NilsM17/all-screen-keyboard-Raspberry/3Dmodels/individualkeys/key29.step

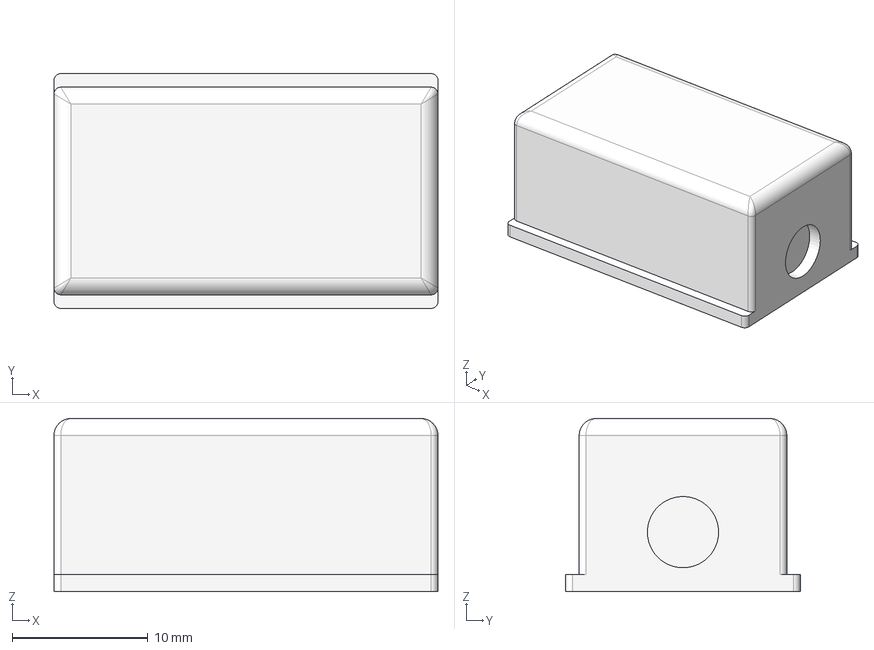
[picture p21: CAD file, 2025-07-11]
3Dmodels/individualkeys/key29.step
28.3 x 17.3 x 12.8 mm
