NilsM17/all-screen-keyboard-Raspberry/3Dmodels/individualkeys/key24.5.step

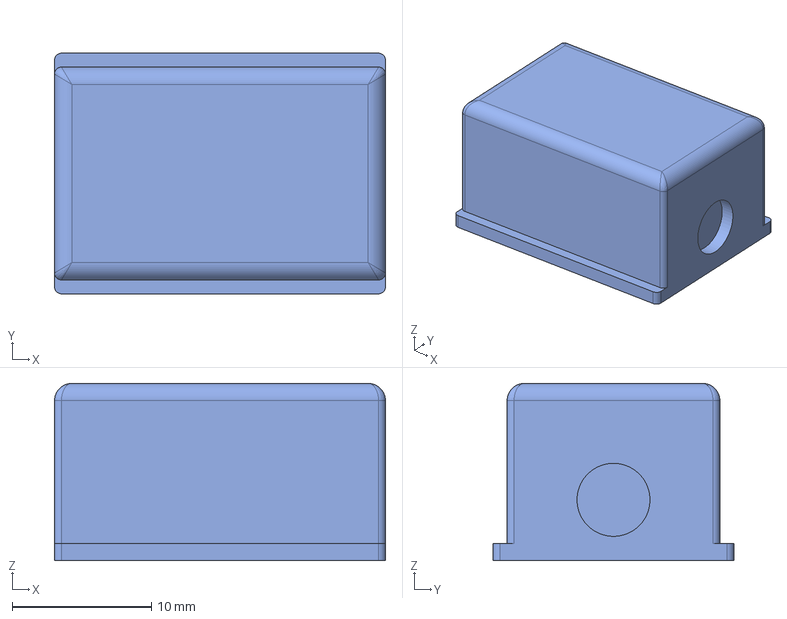
[picture p22: CAD file, 2025-07-11]
3Dmodels/individualkeys/key24.5.step
23.8 x 17.3 x 12.8 mm
