NilsM17/all-screen-keyboard-Raspberry/3Dmodels/individualkeys/key46.step

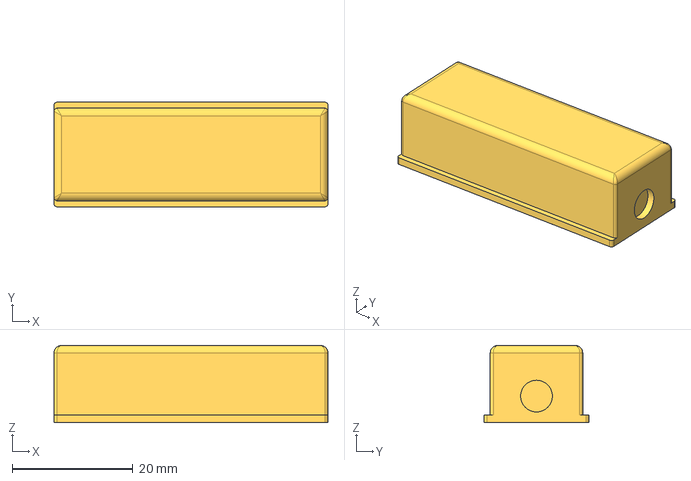
[picture p23: CAD file, 2025-07-11]
3Dmodels/individualkeys/key46.step
45.3 x 17.3 x 12.8 mm
