NilsM17/all-screen-keyboard-Raspberry/3Dmodels/individualkeys/key16.step

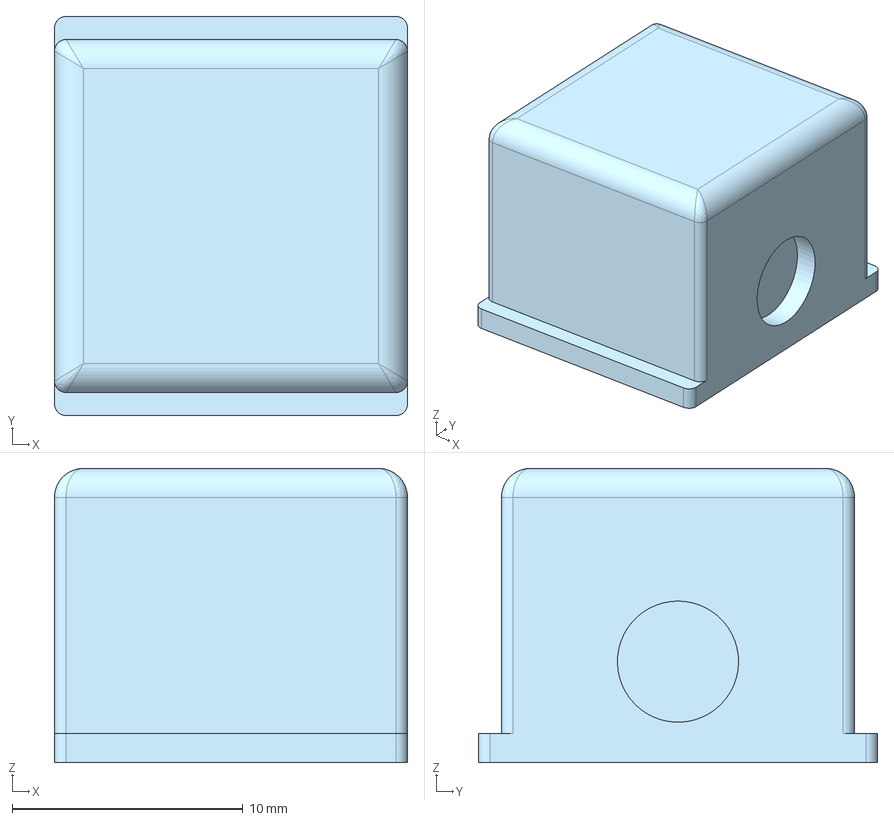
[picture p24: CAD file, 2025-07-11]
3Dmodels/individualkeys/key16.step
15.3 x 17.3 x 12.8 mm
