NilsM17/all-screen-keyboard-Raspberry/PCB/keyboard-KiCad/keyboard.kicad_sch

## KiCad design PCB/keyboard-KiCad/keyboard.kicad_sch (2025-07-11)

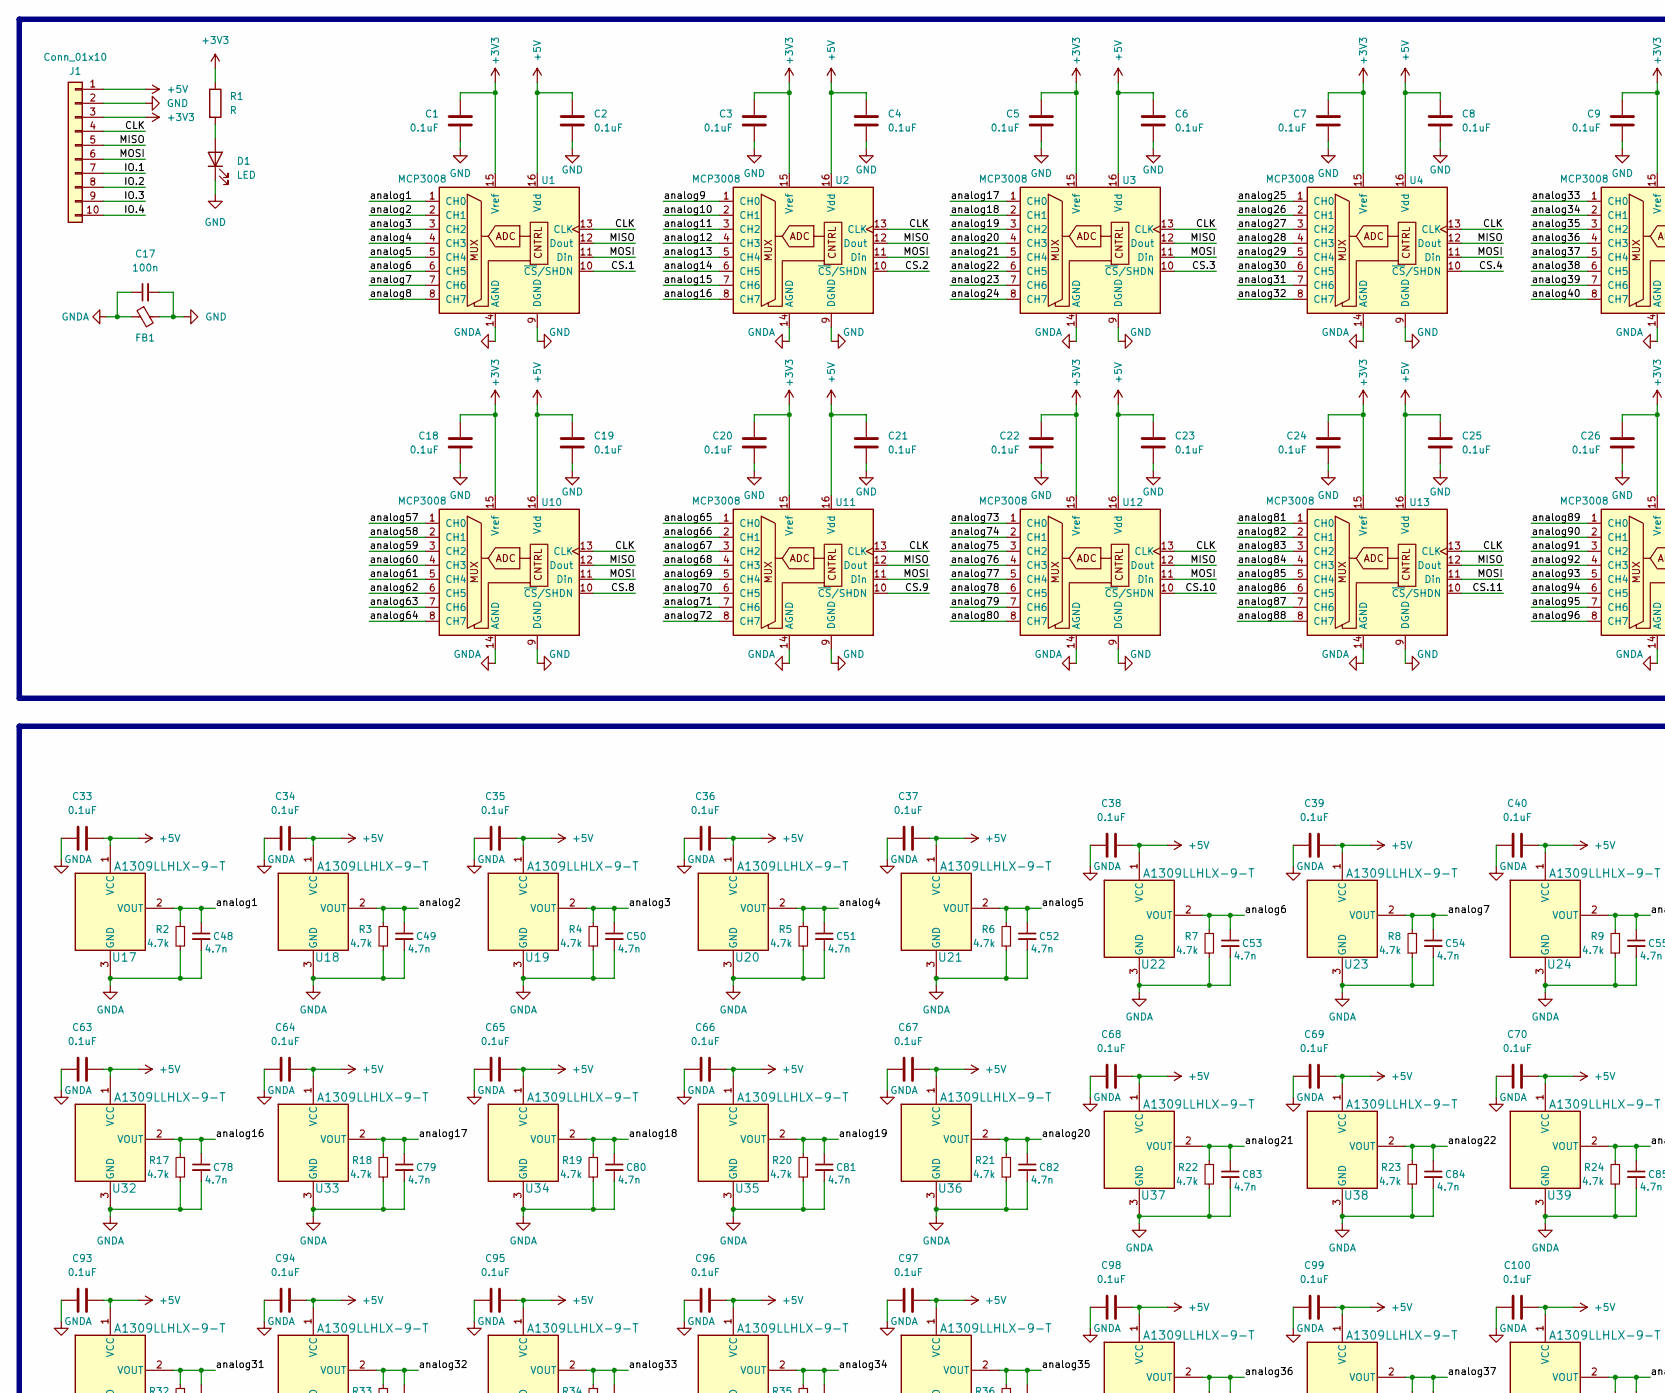
[picture p25: schematic keyboard.kicad_sch, part in row 1, column 1]

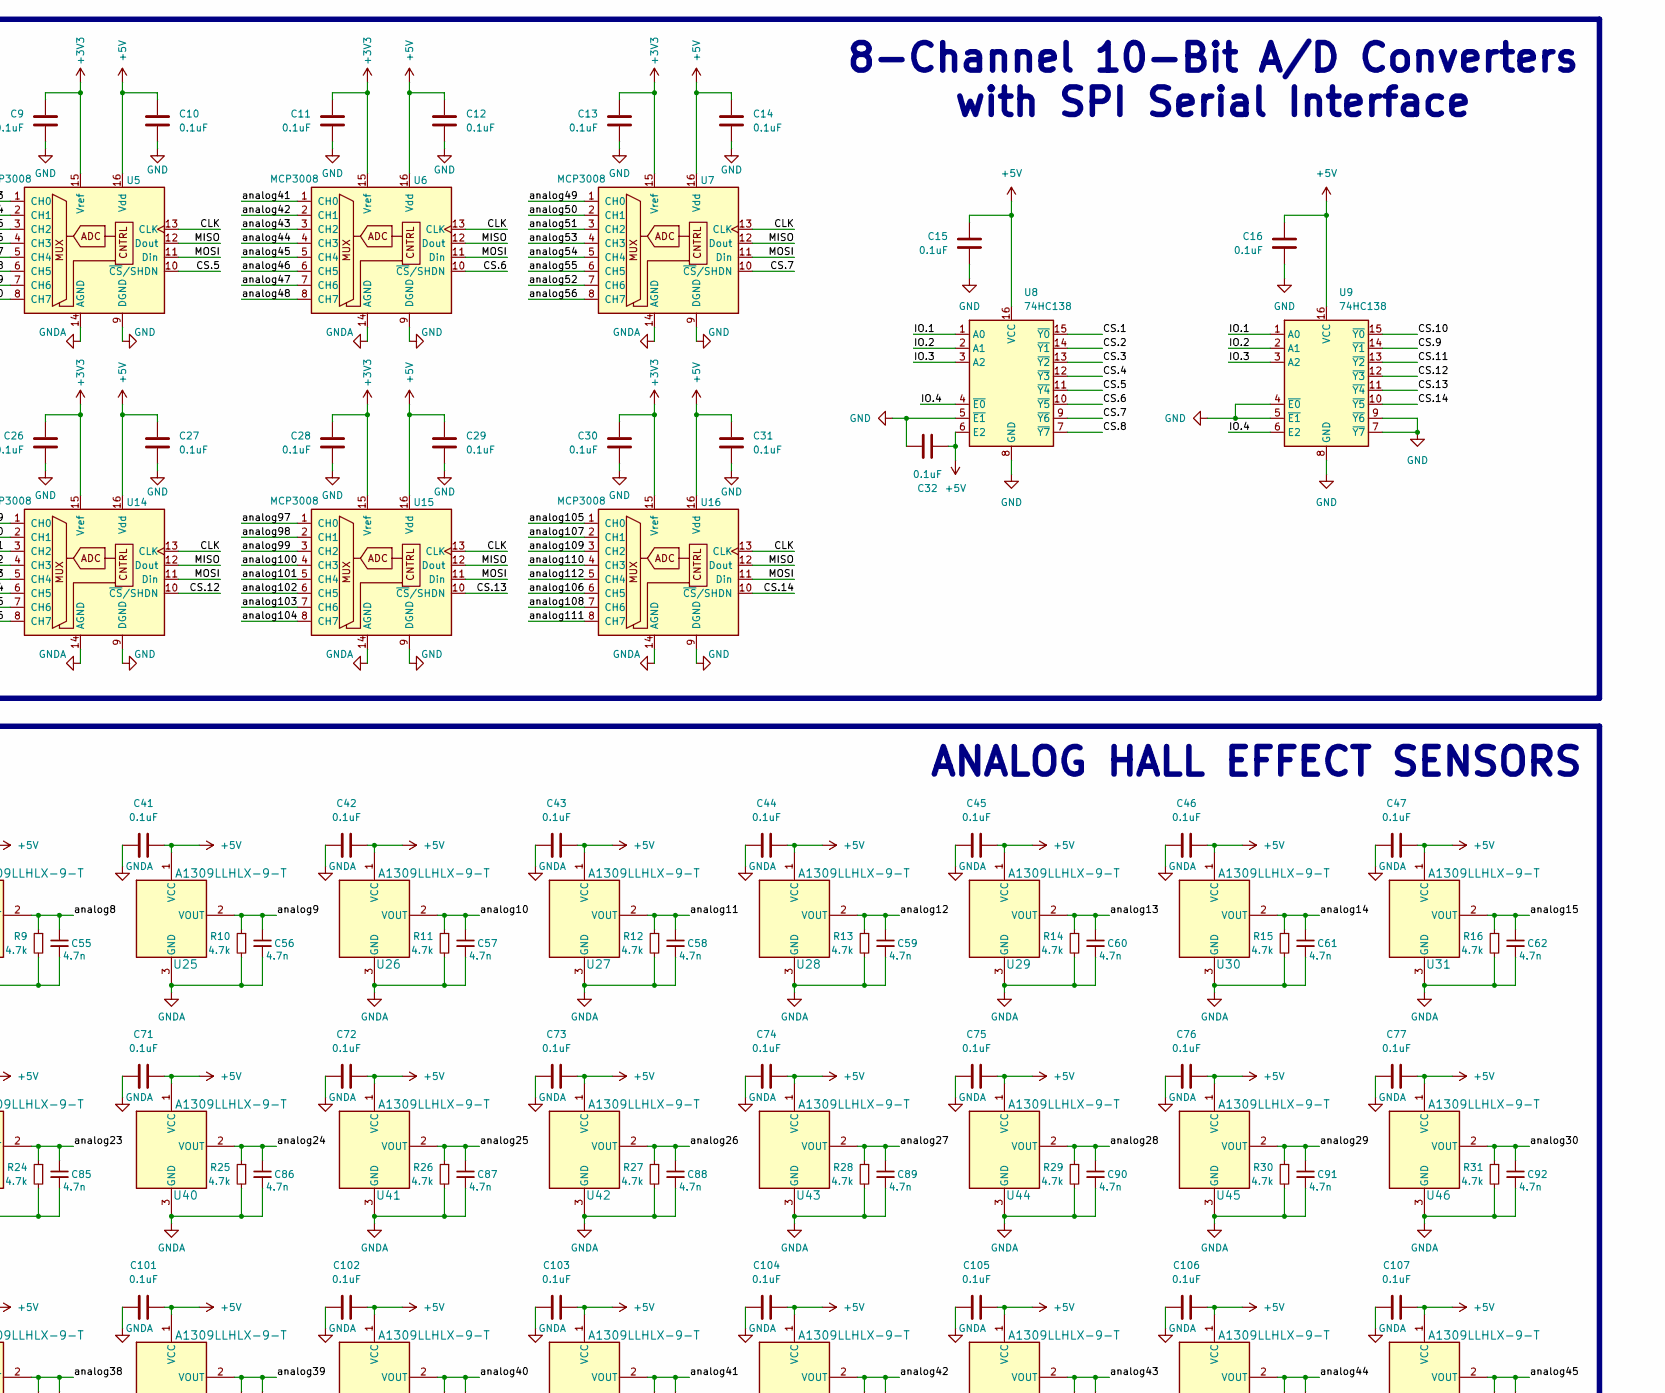
[picture p26: schematic keyboard.kicad_sch, part in row 1, column 2]

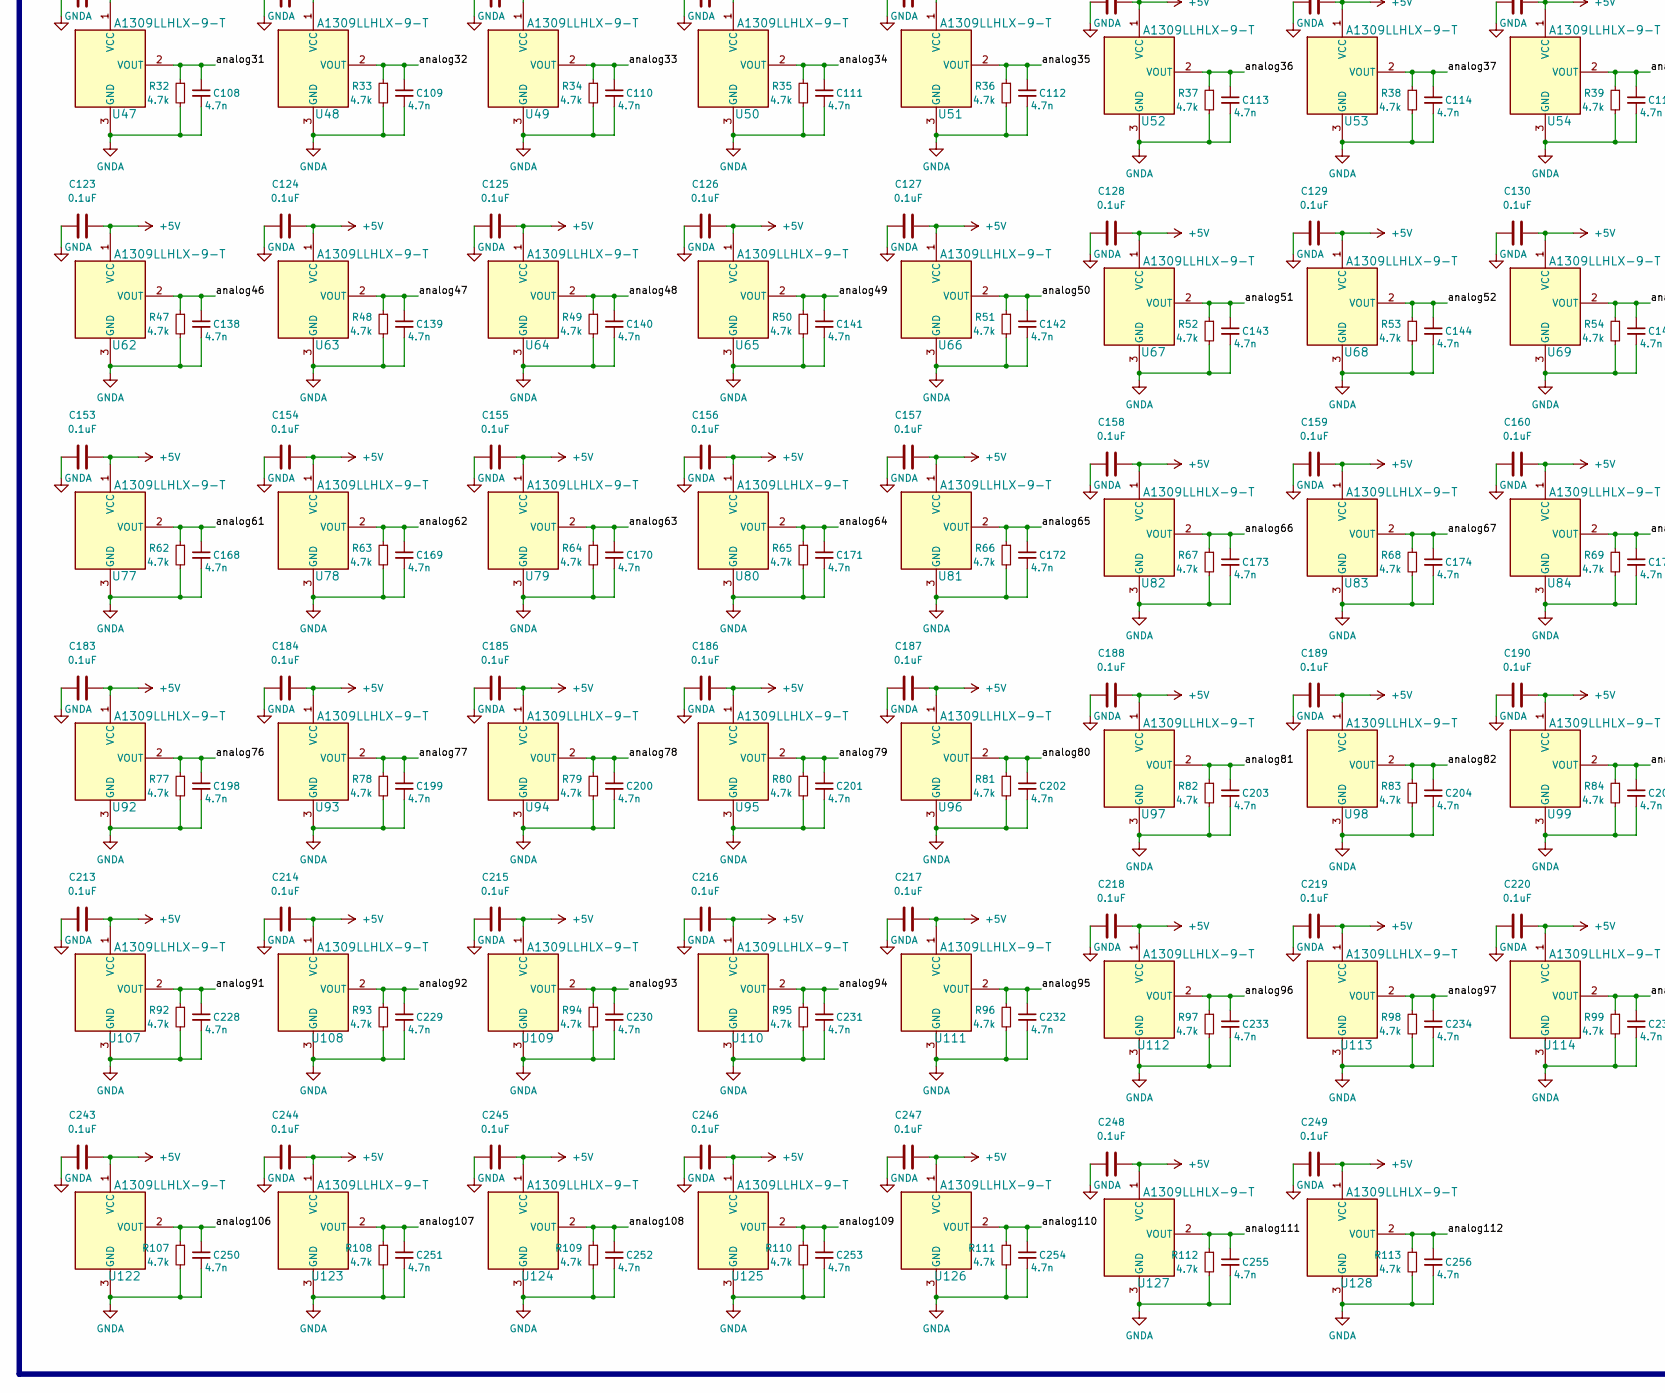
[picture p27: schematic keyboard.kicad_sch, part in row 2, column 1]

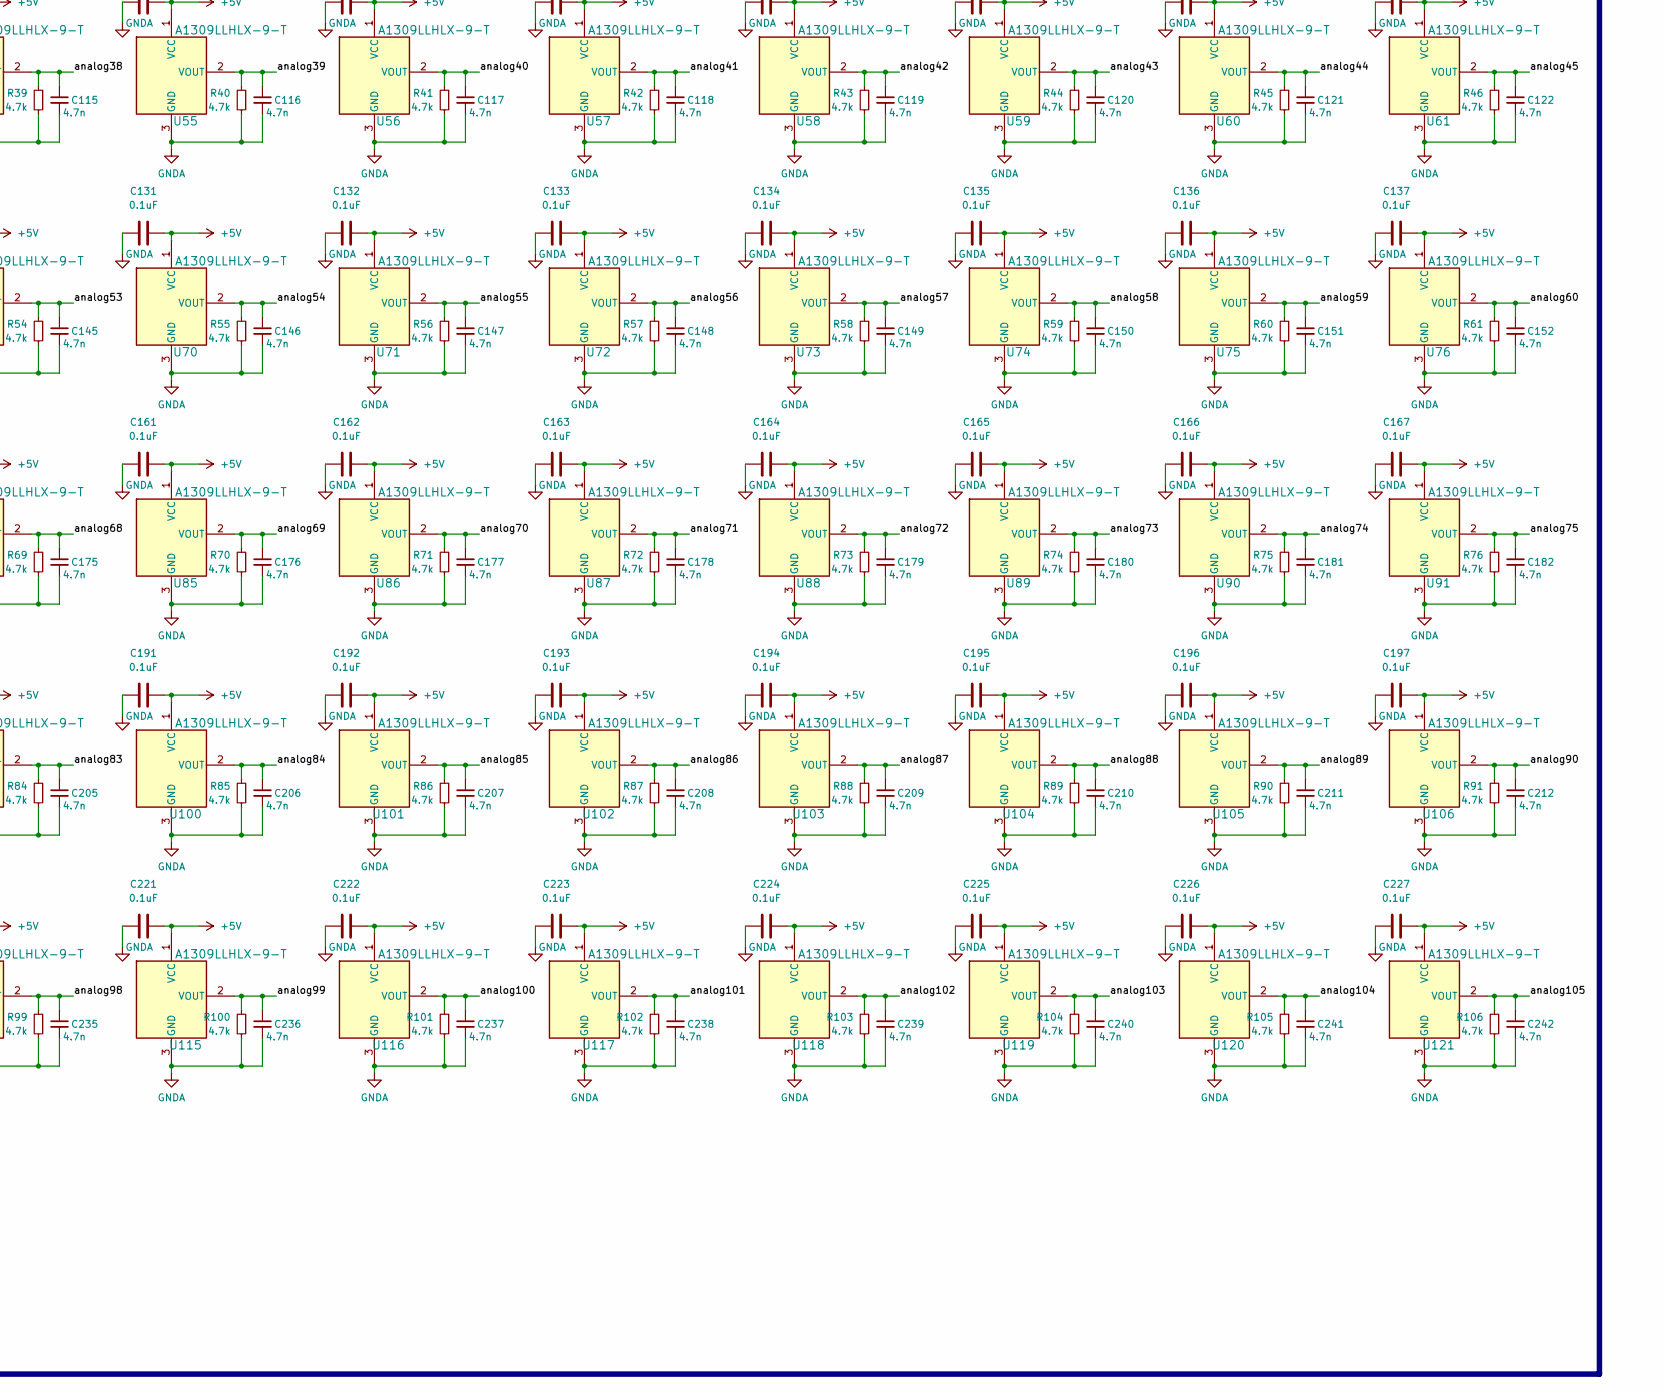
[picture p28: schematic keyboard.kicad_sch, part in row 2, column 2]

Parts:
C1, C2, C3, C4, C5, C6, C7, C8, C9, C10, C11, C12, C13, C14, C15, C16, C18, C19, C20, C21, C22, C23, C24, C25, C26, C27, C28, C29, C30, C31, C32, C33, C34, C35, C36, C37, C38, C39, C40, C41, C42, C43, C44, C45, C46, C47, C63, C64, C65, C66, C67, C68, C69, C70, C71, C72, C73, C74, C75, C76, C77, C93, C94, C95, C96, C97, C98, C99, C100, C101, C102, C103, C104, C105, C106, C107, C123, C124, C125, C126, C127, C128, C129, C130, C131, C132, C133, C134, C135, C136, C137, C153, C154, C155, C156, C157, C158, C159, C160, C161, C162, C163, C164, C165, C166, C167, C183, C184, C185, C186, C187, C188, C189, C190, C191, C192, C193, C194, C195, C196, C197, C213, C214, C215, C216, C217, C218, C219, C220, C221, C222, C223, C224, C225, C226, C227, C243, C244, C245, C246, C247, C248, C249: 0.1uF; C_0603_1608Metric
C17: 100n; C_0603_1608Metric
C48, C49, C50, C51, C52, C53, C54, C55, C56, C57, C58, C59, C60, C61, C62, C78, C79, C80, C81, C82, C83, C84, C85, C86, C87, C88, C89, C90, C91, C92, C108, C109, C110, C111, C112, C113, C114, C115, C116, C117, C118, C119, C120, C121, C122, C138, C139, C140, C141, C142, C143, C144, C145, C146, C147, C148, C149, C150, C151, C152, C168, C169, C170, C171, C172, C173, C174, C175, C176, C177, C178, C179, C180, C181, C182, C198, C199, C200, C201, C202, C203, C204, C205, C206, C207, C208, C209, C210, C211, C212, C228, C229, C230, C231, C232, C233, C234, C235, C236, C237, C238, C239, C240, C241, C242, C250, C251, C252, C253, C254, C255, C256: 4.7n; C_0603_1608Metric
D1: LED; LED_0603_1608Metric
FB1: FerriteBead_Small; L_0603_1608Metric
J1: Conn_01x10; PinHeader_1x10_P2.54mm_Vertical
R1: R; R_0603_1608Metric
R2, R3, R4, R5, R6, R7, R8, R9, R10, R11, R12, R13, R14, R15, R16, R17, R18, R19, R20, R21, R22, R23, R24, R25, R26, R27, R28, R29, R30, R31, R32, R33, R34, R35, R36, R37, R38, R39, R40, R41, R42, R43, R44, R45, R46, R47, R48, R49, R50, R51, R52, R53, R54, R55, R56, R57, R58, R59, R60, R61, R62, R63, R64, R65, R66, R67, R68, R69, R70, R71, R72, R73, R74, R75, R76, R77, R78, R79, R80, R81, R82, R83, R84, R85, R86, R87, R88, R89, R90, R91, R92, R93, R94, R95, R96, R97, R98, R99, R100, R101, R102, R103, R104, R105, R106, R107, R108, R109, R110, R111, R112, R113: 4.7k; R_0603_1608Metric
U1, U2, U3, U4, U5, U6, U7, U10, U11, U12, U13, U14, U15, U16: MCP3008; SOIC16-N_MC_MCH
U8, U9: 74HC138; D0016A_L
U17, U18, U19, U20, U21, U22, U23, U24, U25, U26, U27, U28, U29, U30, U31, U32, U33, U34, U35, U36, U37, U38, U39, U40, U41, U42, U43, U44, U45, U46, U47, U48, U49, U50, U51, U52, U53, U54, U55, U56, U57, U58, U59, U60, U61, U62, U63, U64, U65, U66, U67, U68, U69, U70, U71, U72, U73, U74, U75, U76, U77, U78, U79, U80, U81, U82, U83, U84, U85, U86, U87, U88, U89, U90, U91, U92, U93, U94, U95, U96, U97, U98, U99, U100, U101, U102, U103, U104, U105, U106, U107, U108, U109, U110, U111, U112, U113, U114, U115, U116, U117, U118, U119, U120, U121, U122, U123, U124, U125, U126, U127, U128: A1309LLHLX-9-T; SOT-23W_LH_ALM

Connections:
+3V3: C1.1, C3.1, C5.1, C7.1, C9.1, C11.1, C13.1, C18.1, C20.1, C22.1, C24.1, C26.1, C28.1, C30.1, J1.3, R1.1, U1.15 (Vref), U2.15 (Vref), U3.15 (Vref), U4.15 (Vref), U5.15 (Vref), U6.15 (Vref), U7.15 (Vref), U10.15 (Vref), U11.15 (Vref), U12.15 (Vref), U13.15 (Vref), U14.15 (Vref), U15.15 (Vref), U16.15 (Vref)
+5V: C2.1, C4.1, C6.1, C8.1, C10.1, C12.1, C14.1, C15.1, C16.1, C19.1, C21.1, C23.1, C25.1, C27.1, C29.1, C31.1, C32.2, C33.2, C34.2, C35.2, C36.2, C37.2, C38.2, C39.2, C40.2, C41.2, C42.2, C43.2, C44.2, C45.2, C46.2, C47.2, C63.2, C64.2, C65.2, C66.2, C67.2, C68.2, C69.2, C70.2, C71.2, C72.2, C73.2, C74.2, C75.2, C76.2, C77.2, C93.2, C94.2, C95.2, C96.2, C97.2, C98.2, C99.2, C100.2, C101.2, C102.2, C103.2, C104.2, C105.2, C106.2, C107.2, C123.2, C124.2, C125.2, C126.2, C127.2, C128.2, C129.2, C130.2, C131.2, C132.2, C133.2, C134.2, C135.2, C136.2, C137.2, C153.2, C154.2, C155.2, C156.2, C157.2, C158.2, C159.2, C160.2, C161.2, C162.2, C163.2, C164.2, C165.2, C166.2, C167.2, C183.2, C184.2, C185.2, C186.2, C187.2, C188.2, C189.2, C190.2, C191.2, C192.2, C193.2, C194.2, C195.2, C196.2, C197.2, C213.2, C214.2, C215.2, C216.2, C217.2, C218.2, C219.2, C220.2, C221.2, C222.2, C223.2, C224.2, C225.2, C226.2, C227.2, C243.2, C244.2, C245.2, C246.2, C247.2, C248.2, C249.2, J1.1, U1.16 (Vdd), U2.16 (Vdd), U3.16 (Vdd), U4.16 (Vdd), U5.16 (Vdd), U6.16 (Vdd), U7.16 (Vdd), U8.6 (E2), U8.16 (VCC), U9.16 (VCC), U10.16 (Vdd), U11.16 (Vdd), U12.16 (Vdd), U13.16 (Vdd), U14.16 (Vdd), U15.16 (Vdd), U16.16 (Vdd), U17.1 (VCC), U18.1 (VCC), U19.1 (VCC), U20.1 (VCC), U21.1 (VCC), U22.1 (VCC), U23.1 (VCC), U24.1 (VCC), U25.1 (VCC), U26.1 (VCC), U27.1 (VCC), U28.1 (VCC), U29.1 (VCC), U30.1 (VCC), U31.1 (VCC), U32.1 (VCC), U33.1 (VCC), U34.1 (VCC), U35.1 (VCC), U36.1 (VCC), U37.1 (VCC), U38.1 (VCC), U39.1 (VCC), U40.1 (VCC), U41.1 (VCC), U42.1 (VCC), U43.1 (VCC), U44.1 (VCC), U45.1 (VCC), U46.1 (VCC), U47.1 (VCC), U48.1 (VCC), U49.1 (VCC), U50.1 (VCC), U51.1 (VCC), U52.1 (VCC), U53.1 (VCC), U54.1 (VCC), U55.1 (VCC), U56.1 (VCC), U57.1 (VCC), U58.1 (VCC), U59.1 (VCC), U60.1 (VCC), U61.1 (VCC), U62.1 (VCC), U63.1 (VCC), U64.1 (VCC), U65.1 (VCC), U66.1 (VCC), U67.1 (VCC), U68.1 (VCC), U69.1 (VCC), U70.1 (VCC), U71.1 (VCC), U72.1 (VCC), U73.1 (VCC), U74.1 (VCC), U75.1 (VCC), U76.1 (VCC), U77.1 (VCC), U78.1 (VCC), U79.1 (VCC), U80.1 (VCC), U81.1 (VCC), U82.1 (VCC), U83.1 (VCC), U84.1 (VCC), U85.1 (VCC), U86.1 (VCC), U87.1 (VCC), U88.1 (VCC), U89.1 (VCC), U90.1 (VCC), U91.1 (VCC), U92.1 (VCC), U93.1 (VCC), U94.1 (VCC), U95.1 (VCC), U96.1 (VCC), U97.1 (VCC), U98.1 (VCC), U99.1 (VCC), U100.1 (VCC), U101.1 (VCC), U102.1 (VCC), U103.1 (VCC), U104.1 (VCC), U105.1 (VCC), U106.1 (VCC), U107.1 (VCC), U108.1 (VCC), U109.1 (VCC), U110.1 (VCC), U111.1 (VCC), U112.1 (VCC), U113.1 (VCC), U114.1 (VCC), U115.1 (VCC), U116.1 (VCC), U117.1 (VCC), U118.1 (VCC), U119.1 (VCC), U120.1 (VCC), U121.1 (VCC), U122.1 (VCC), U123.1 (VCC), U124.1 (VCC), U125.1 (VCC), U126.1 (VCC), U127.1 (VCC), U128.1 (VCC)
CLK: J1.4, U1.13 (CLK), U2.13 (CLK), U3.13 (CLK), U4.13 (CLK), U5.13 (CLK), U6.13 (CLK), U7.13 (CLK), U10.13 (CLK), U11.13 (CLK), U12.13 (CLK), U13.13 (CLK), U14.13 (CLK), U15.13 (CLK), U16.13 (CLK)
CS.1: U1.10 (~CS/SHDN), U8.15 (~Y0)
CS.2: U2.10 (~CS/SHDN), U8.14 (~Y1)
CS.3: U3.10 (~CS/SHDN), U8.13 (~Y2)
CS.4: U4.10 (~CS/SHDN), U8.12 (~Y3)
CS.5: U5.10 (~CS/SHDN), U8.11 (~Y4)
CS.6: U6.10 (~CS/SHDN), U8.10 (~Y5)
CS.7: U7.10 (~CS/SHDN), U8.9 (~Y6)
CS.8: U8.7 (~Y7), U10.10 (~CS/SHDN)
CS.9: U9.14 (~Y1), U11.10 (~CS/SHDN)
CS.10: U9.15 (~Y0), U12.10 (~CS/SHDN)
CS.11: U9.13 (~Y2), U13.10 (~CS/SHDN)
CS.12: U9.12 (~Y3), U14.10 (~CS/SHDN)
CS.13: U9.11 (~Y4), U15.10 (~CS/SHDN)
CS.14: U9.10 (~Y5), U16.10 (~CS/SHDN)
GND: C1.2, C2.2, C3.2, C4.2, C5.2, C6.2, C7.2, C8.2, C9.2, C10.2, C11.2, C12.2, C13.2, C14.2, C15.2, C16.2, C17.2, C18.2, C19.2, C20.2, C21.2, C22.2, C23.2, C24.2, C25.2, C26.2, C27.2, C28.2, C29.2, C30.2, C31.2, C32.1, D1.1 (K), FB1.2, J1.2, U1.9 (DGND), U2.9 (DGND), U3.9 (DGND), U4.9 (DGND), U5.9 (DGND), U6.9 (DGND), U7.9 (DGND), U8.5 (~E1), U8.8 (GND), U9.4 (~E0), U9.5 (~E1), U9.7 (~Y7), U9.8 (GND), U9.9 (~Y6), U10.9 (DGND), U11.9 (DGND), U12.9 (DGND), U13.9 (DGND), U14.9 (DGND), U15.9 (DGND), U16.9 (DGND)
GNDA: C17.1, C33.1, C34.1, C35.1, C36.1, C37.1, C38.1, C39.1, C40.1, C41.1, C42.1, C43.1, C44.1, C45.1, C46.1, C47.1, C48.2, C49.2, C50.2, C51.2, C52.2, C53.2, C54.2, C55.2, C56.2, C57.2, C58.2, C59.2, C60.2, C61.2, C62.2, C63.1, C64.1, C65.1, C66.1, C67.1, C68.1, C69.1, C70.1, C71.1, C72.1, C73.1, C74.1, C75.1, C76.1, C77.1, C78.2, C79.2, C80.2, C81.2, C82.2, C83.2, C84.2, C85.2, C86.2, C87.2, C88.2, C89.2, C90.2, C91.2, C92.2, C93.1, C94.1, C95.1, C96.1, C97.1, C98.1, C99.1, C100.1, C101.1, C102.1, C103.1, C104.1, C105.1, C106.1, C107.1, C108.2, C109.2, C110.2, C111.2, C112.2, C113.2, C114.2, C115.2, C116.2, C117.2, C118.2, C119.2, C120.2, C121.2, C122.2, C123.1, C124.1, C125.1, C126.1, C127.1, C128.1, C129.1, C130.1, C131.1, C132.1, C133.1, C134.1, C135.1, C136.1, C137.1, C138.2, C139.2, C140.2, C141.2, C142.2, C143.2, C144.2, C145.2, C146.2, C147.2, C148.2, C149.2, C150.2, C151.2, C152.2, C153.1, C154.1, C155.1, C156.1, C157.1, C158.1, C159.1, C160.1, C161.1, C162.1, C163.1, C164.1, C165.1, C166.1, C167.1, C168.2, C169.2, C170.2, C171.2, C172.2, C173.2, C174.2, C175.2, C176.2, C177.2, C178.2, C179.2, C180.2, C181.2, C182.2, C183.1, C184.1, C185.1, C186.1, C187.1, C188.1, C189.1, C190.1, C191.1, C192.1, C193.1, C194.1, C195.1, C196.1, C197.1, C198.2, C199.2, C200.2, C201.2, C202.2, C203.2, C204.2, C205.2, C206.2, C207.2, C208.2, C209.2, C210.2, C211.2, C212.2, C213.1, C214.1, C215.1, C216.1, C217.1, C218.1, C219.1, C220.1, C221.1, C222.1, C223.1, C224.1, C225.1, C226.1, C227.1, C228.2, C229.2, C230.2, C231.2, C232.2, C233.2, C234.2, C235.2, C236.2, C237.2, C238.2, C239.2, C240.2, C241.2, C242.2, C243.1, C244.1, C245.1, C246.1, C247.1, C248.1, C249.1, C250.2, C251.2, C252.2, C253.2, C254.2, C255.2, C256.2, FB1.1, R2.2, R3.2, R4.2, R5.2, R6.2, R7.2, R8.2, R9.2, R10.2, R11.2, R12.2, R13.2, R14.2, R15.2, R16.2, R17.2, R18.2, R19.2, R20.2, R21.2, R22.2, R23.2, R24.2, R25.2, R26.2, R27.2, R28.2, R29.2, R30.2, R31.2, R32.2, R33.2, R34.2, R35.2, R36.2, R37.2, R38.2, R39.2, R40.2, R41.2, R42.2, R43.2, R44.2, R45.2, R46.2, R47.2, R48.2, R49.2, R50.2, R51.2, R52.2, R53.2, R54.2, R55.2, R56.2, R57.2, R58.2, R59.2, R60.2, R61.2, R62.2, R63.2, R64.2, R65.2, R66.2, R67.2, R68.2, R69.2, R70.2, R71.2, R72.2, R73.2, R74.2, R75.2, R76.2, R77.2, R78.2, R79.2, R80.2, R81.2, R82.2, R83.2, R84.2, R85.2, R86.2, R87.2, R88.2, R89.2, R90.2, R91.2, R92.2, R93.2, R94.2, R95.2, R96.2, R97.2, R98.2, R99.2, R100.2, R101.2, R102.2, R103.2, R104.2, R105.2, R106.2, R107.2, R108.2, R109.2, R110.2, R111.2, R112.2, R113.2, U1.14 (AGND), U2.14 (AGND), U3.14 (AGND), U4.14 (AGND), U5.14 (AGND), U6.14 (AGND), U7.14 (AGND), U10.14 (AGND), U11.14 (AGND), U12.14 (AGND), U13.14 (AGND), U14.14 (AGND), U15.14 (AGND), U16.14 (AGND), U17.3 (GND), U18.3 (GND), U19.3 (GND), U20.3 (GND), U21.3 (GND), U22.3 (GND), U23.3 (GND), U24.3 (GND), U25.3 (GND), U26.3 (GND), U27.3 (GND), U28.3 (GND), U29.3 (GND), U30.3 (GND), U31.3 (GND), U32.3 (GND), U33.3 (GND), U34.3 (GND), U35.3 (GND), U36.3 (GND), U37.3 (GND), U38.3 (GND), U39.3 (GND), U40.3 (GND), U41.3 (GND), U42.3 (GND), U43.3 (GND), U44.3 (GND), U45.3 (GND), U46.3 (GND), U47.3 (GND), U48.3 (GND), U49.3 (GND), U50.3 (GND), U51.3 (GND), U52.3 (GND), U53.3 (GND), U54.3 (GND), U55.3 (GND), U56.3 (GND), U57.3 (GND), U58.3 (GND), U59.3 (GND), U60.3 (GND), U61.3 (GND), U62.3 (GND), U63.3 (GND), U64.3 (GND), U65.3 (GND), U66.3 (GND), U67.3 (GND), U68.3 (GND), U69.3 (GND), U70.3 (GND), U71.3 (GND), U72.3 (GND), U73.3 (GND), U74.3 (GND), U75.3 (GND), U76.3 (GND), U77.3 (GND), U78.3 (GND), U79.3 (GND), U80.3 (GND), U81.3 (GND), U82.3 (GND), U83.3 (GND), U84.3 (GND), U85.3 (GND), U86.3 (GND), U87.3 (GND), U88.3 (GND), U89.3 (GND), U90.3 (GND), U91.3 (GND), U92.3 (GND), U93.3 (GND), U94.3 (GND), U95.3 (GND), U96.3 (GND), U97.3 (GND), U98.3 (GND), U99.3 (GND), U100.3 (GND), U101.3 (GND), U102.3 (GND), U103.3 (GND), U104.3 (GND), U105.3 (GND), U106.3 (GND), U107.3 (GND), U108.3 (GND), U109.3 (GND), U110.3 (GND), U111.3 (GND), U112.3 (GND), U113.3 (GND), U114.3 (GND), U115.3 (GND), U116.3 (GND), U117.3 (GND), U118.3 (GND), U119.3 (GND), U120.3 (GND), U121.3 (GND), U122.3 (GND), U123.3 (GND), U124.3 (GND), U125.3 (GND), U126.3 (GND), U127.3 (GND), U128.3 (GND)
IO.1: J1.7, U8.1 (A0), U9.1 (A0)
IO.2: J1.8, U8.2 (A1), U9.2 (A1)
IO.3: J1.9, U8.3 (A2), U9.3 (A2)
IO.4: J1.10, U8.4 (~E0), U9.6 (E2)
MISO: J1.5, U1.12 (Dout), U2.12 (Dout), U3.12 (Dout), U4.12 (Dout), U5.12 (Dout), U6.12 (Dout), U7.12 (Dout), U10.12 (Dout), U11.12 (Dout), U12.12 (Dout), U13.12 (Dout), U14.12 (Dout), U15.12 (Dout), U16.12 (Dout)
MOSI: J1.6, U1.11 (Din), U2.11 (Din), U3.11 (Din), U4.11 (Din), U5.11 (Din), U6.11 (Din), U7.11 (Din), U10.11 (Din), U11.11 (Din), U12.11 (Din), U13.11 (Din), U14.11 (Din), U15.11 (Din), U16.11 (Din)
unnamed: D1.2 (A), R1.2
analog1: C48.1, R2.1, U1.1 (CH0), U17.2 (VOUT)
analog2: C49.1, R3.1, U1.2 (CH1), U18.2 (VOUT)
analog3: C50.1, R4.1, U1.3 (CH2), U19.2 (VOUT)
analog4: C51.1, R5.1, U1.4 (CH3), U20.2 (VOUT)
analog5: C52.1, R6.1, U1.5 (CH4), U21.2 (VOUT)
analog6: C53.1, R7.1, U1.6 (CH5), U22.2 (VOUT)
analog7: C54.1, R8.1, U1.7 (CH6), U23.2 (VOUT)
analog8: C55.1, R9.1, U1.8 (CH7), U24.2 (VOUT)
analog9: C56.1, R10.1, U2.1 (CH0), U25.2 (VOUT)
analog10: C57.1, R11.1, U2.2 (CH1), U26.2 (VOUT)
analog11: C58.1, R12.1, U2.3 (CH2), U27.2 (VOUT)
analog12: C59.1, R13.1, U2.4 (CH3), U28.2 (VOUT)
analog13: C60.1, R14.1, U2.5 (CH4), U29.2 (VOUT)
analog14: C61.1, R15.1, U2.6 (CH5), U30.2 (VOUT)
analog15: C62.1, R16.1, U2.7 (CH6), U31.2 (VOUT)
analog16: C78.1, R17.1, U2.8 (CH7), U32.2 (VOUT)
analog17: C79.1, R18.1, U3.1 (CH0), U33.2 (VOUT)
analog18: C80.1, R19.1, U3.2 (CH1), U34.2 (VOUT)
analog19: C81.1, R20.1, U3.3 (CH2), U35.2 (VOUT)
analog20: C82.1, R21.1, U3.4 (CH3), U36.2 (VOUT)
analog21: C83.1, R22.1, U3.5 (CH4), U37.2 (VOUT)
analog22: C84.1, R23.1, U3.6 (CH5), U38.2 (VOUT)
analog23: C85.1, R24.1, U3.7 (CH6), U39.2 (VOUT)
analog24: C86.1, R25.1, U3.8 (CH7), U40.2 (VOUT)
analog25: C87.1, R26.1, U4.1 (CH0), U41.2 (VOUT)
analog26: C88.1, R27.1, U4.2 (CH1), U42.2 (VOUT)
analog27: C89.1, R28.1, U4.3 (CH2), U43.2 (VOUT)
analog28: C90.1, R29.1, U4.4 (CH3), U44.2 (VOUT)
analog29: C91.1, R30.1, U4.5 (CH4), U45.2 (VOUT)
analog30: C92.1, R31.1, U4.6 (CH5), U46.2 (VOUT)
analog31: C108.1, R32.1, U4.7 (CH6), U47.2 (VOUT)
analog32: C109.1, R33.1, U4.8 (CH7), U48.2 (VOUT)
analog33: C110.1, R34.1, U5.1 (CH0), U49.2 (VOUT)
analog34: C111.1, R35.1, U5.2 (CH1), U50.2 (VOUT)
analog35: C112.1, R36.1, U5.3 (CH2), U51.2 (VOUT)
analog36: C113.1, R37.1, U5.4 (CH3), U52.2 (VOUT)
analog37: C114.1, R38.1, U5.5 (CH4), U53.2 (VOUT)
analog38: C115.1, R39.1, U5.6 (CH5), U54.2 (VOUT)
analog39: C116.1, R40.1, U5.7 (CH6), U55.2 (VOUT)
analog40: C117.1, R41.1, U5.8 (CH7), U56.2 (VOUT)
analog41: C118.1, R42.1, U6.1 (CH0), U57.2 (VOUT)
analog42: C119.1, R43.1, U6.2 (CH1), U58.2 (VOUT)
analog43: C120.1, R44.1, U6.3 (CH2), U59.2 (VOUT)
analog44: C121.1, R45.1, U6.4 (CH3), U60.2 (VOUT)
analog45: C122.1, R46.1, U6.5 (CH4), U61.2 (VOUT)
analog46: C138.1, R47.1, U6.6 (CH5), U62.2 (VOUT)
analog47: C139.1, R48.1, U6.7 (CH6), U63.2 (VOUT)
analog48: C140.1, R49.1, U6.8 (CH7), U64.2 (VOUT)
analog49: C141.1, R50.1, U7.1 (CH0), U65.2 (VOUT)
analog50: C142.1, R51.1, U7.2 (CH1), U66.2 (VOUT)
analog51: C143.1, R52.1, U7.3 (CH2), U67.2 (VOUT)
analog52: C144.1, R53.1, U7.7 (CH6), U68.2 (VOUT)
analog53: C145.1, R54.1, U7.4 (CH3), U69.2 (VOUT)
analog54: C146.1, R55.1, U7.5 (CH4), U70.2 (VOUT)
analog55: C147.1, R56.1, U7.6 (CH5), U71.2 (VOUT)
analog56: C148.1, R57.1, U7.8 (CH7), U72.2 (VOUT)
analog57: C149.1, R58.1, U10.1 (CH0), U73.2 (VOUT)
analog58: C150.1, R59.1, U10.2 (CH1), U74.2 (VOUT)
analog59: C151.1, R60.1, U10.3 (CH2), U75.2 (VOUT)
analog60: C152.1, R61.1, U10.4 (CH3), U76.2 (VOUT)
analog61: C168.1, R62.1, U10.5 (CH4), U77.2 (VOUT)
analog62: C169.1, R63.1, U10.6 (CH5), U78.2 (VOUT)
analog63: C170.1, R64.1, U10.7 (CH6), U79.2 (VOUT)
analog64: C171.1, R65.1, U10.8 (CH7), U80.2 (VOUT)
analog65: C172.1, R66.1, U11.1 (CH0), U81.2 (VOUT)
analog66: C173.1, R67.1, U11.2 (CH1), U82.2 (VOUT)
analog67: C174.1, R68.1, U11.3 (CH2), U83.2 (VOUT)
analog68: C175.1, R69.1, U11.4 (CH3), U84.2 (VOUT)
analog69: C176.1, R70.1, U11.5 (CH4), U85.2 (VOUT)
analog70: C177.1, R71.1, U11.6 (CH5), U86.2 (VOUT)
analog71: C178.1, R72.1, U11.7 (CH6), U87.2 (VOUT)
analog72: C179.1, R73.1, U11.8 (CH7), U88.2 (VOUT)
analog73: C180.1, R74.1, U12.1 (CH0), U89.2 (VOUT)
analog74: C181.1, R75.1, U12.2 (CH1), U90.2 (VOUT)
analog75: C182.1, R76.1, U12.3 (CH2), U91.2 (VOUT)
analog76: C198.1, R77.1, U12.4 (CH3), U92.2 (VOUT)
analog77: C199.1, R78.1, U12.5 (CH4), U93.2 (VOUT)
analog78: C200.1, R79.1, U12.6 (CH5), U94.2 (VOUT)
analog79: C201.1, R80.1, U12.7 (CH6), U95.2 (VOUT)
analog80: C202.1, R81.1, U12.8 (CH7), U96.2 (VOUT)
analog81: C203.1, R82.1, U13.1 (CH0), U97.2 (VOUT)
analog82: C204.1, R83.1, U13.2 (CH1), U98.2 (VOUT)
analog83: C205.1, R84.1, U13.3 (CH2), U99.2 (VOUT)
analog84: C206.1, R85.1, U13.4 (CH3), U100.2 (VOUT)
analog85: C207.1, R86.1, U13.5 (CH4), U101.2 (VOUT)
analog86: C208.1, R87.1, U13.6 (CH5), U102.2 (VOUT)
analog87: C209.1, R88.1, U13.7 (CH6), U103.2 (VOUT)
analog88: C210.1, R89.1, U13.8 (CH7), U104.2 (VOUT)
analog89: C211.1, R90.1, U14.1 (CH0), U105.2 (VOUT)
analog90: C212.1, R91.1, U14.2 (CH1), U106.2 (VOUT)
analog91: C228.1, R92.1, U14.3 (CH2), U107.2 (VOUT)
analog92: C229.1, R93.1, U14.4 (CH3), U108.2 (VOUT)
analog93: C230.1, R94.1, U14.5 (CH4), U109.2 (VOUT)
analog94: C231.1, R95.1, U14.6 (CH5), U110.2 (VOUT)
analog95: C232.1, R96.1, U14.7 (CH6), U111.2 (VOUT)
analog96: C233.1, R97.1, U14.8 (CH7), U112.2 (VOUT)
analog97: C234.1, R98.1, U15.1 (CH0), U113.2 (VOUT)
analog98: C235.1, R99.1, U15.2 (CH1), U114.2 (VOUT)
analog99: C236.1, R100.1, U15.3 (CH2), U115.2 (VOUT)
analog100: C237.1, R101.1, U15.4 (CH3), U116.2 (VOUT)
analog101: C238.1, R102.1, U15.5 (CH4), U117.2 (VOUT)
analog102: C239.1, R103.1, U15.6 (CH5), U118.2 (VOUT)
analog103: C240.1, R104.1, U15.7 (CH6), U119.2 (VOUT)
analog104: C241.1, R105.1, U15.8 (CH7), U120.2 (VOUT)
analog105: C242.1, R106.1, U16.1 (CH0), U121.2 (VOUT)
analog106: C250.1, R107.1, U16.6 (CH5), U122.2 (VOUT)
analog107: C251.1, R108.1, U16.2 (CH1), U123.2 (VOUT)
analog108: C252.1, R109.1, U16.7 (CH6), U124.2 (VOUT)
analog109: C253.1, R110.1, U16.3 (CH2), U125.2 (VOUT)
analog110: C254.1, R111.1, U16.4 (CH3), U126.2 (VOUT)
analog111: C255.1, R112.1, U16.8 (CH7), U127.2 (VOUT)
analog112: C256.1, R113.1, U16.5 (CH4), U128.2 (VOUT)

Notes on the sheet:
ANALOG HALL EFFECT SENSORS
8-Channel 10-Bit A/D Converters with SPI Serial Interface
