NilsM17/all-screen-keyboard-Raspberry/keyboard/src/physicalLayout.cpp

//physicalLayout.cpp

#include "physicalLayout.h"

using namespace std;

const float keyboardWidth = 2560.0f;
const float keyboardHeight = 1440.0f;

const int keyboardWidthPhysical = 382.0f;	//mm
const int keyboardHeightPhysical = 210.0f;	//mm

vector<physicalLayout::keyRect> physicalLayout::getPhysicalKeySizes(){
	vector<physicalLayout::keyRect> keyrects;
	
	//starting from the bottom up
	float lo = (1.5f / keyboardWidthPhysical) * keyboardWidth;	//left offset
	float ho = -20.0f;	//height offset
	float keyGapH = (2.0f / keyboardHeightPhysical) * keyboardHeight;	//~13.7
	float keyGapW = (1.0f / keyboardHeightPhysical) * keyboardHeight;
	float keyGapWide = (4.0f / keyboardHeightPhysical) * keyboardHeight;
	float keyHeight = (16.0f / keyboardHeightPhysical) * keyboardHeight;
	float keyWidth = (16.0f / keyboardWidthPhysical) * keyboardWidth;
	float tabWidth = (24.5f / keyboardWidthPhysical) * keyboardWidth;
	float capsWidth = (29.0f / keyboardWidthPhysical) * keyboardWidth;
	float leftShiftWidth = (37.0f / keyboardWidthPhysical) * keyboardWidth;
	float shiftWidth = (46.0f / keyboardWidthPhysical) * keyboardWidth;
	float ctrlWidth = (20.0f / keyboardWidthPhysical) * keyboardWidth;
	float bottomFnWidth = (27.0f / keyboardWidthPhysical) * keyboardWidth;
	float backspaceWidth = (33.0f / keyboardWidthPhysical) * keyboardWidth;
	float spacebarWidth = (100.0f / keyboardWidthPhysical) * keyboardWidth;
	float verticalHeight = (34.0f / keyboardHeightPhysical) * keyboardHeight;
	float rowGapBig = (6.0f / keyboardHeightPhysical) * keyboardHeight;
	float fnKeyGap = (10.5f / keyboardWidthPhysical) * keyboardWidth;

	//row 6 main keys:
	keyrects.push_back(makeRect((lo), ((keyboardHeight - keyGapH) - keyHeight) - ho, (ctrlWidth), (keyHeight)));
	keyrects.push_back(makeRect((lo + keyGapW + ctrlWidth), ((keyboardHeight - keyGapH) - keyHeight) - ho, (ctrlWidth), (keyHeight)));
	keyrects.push_back(makeRect((lo + keyGapW*2 + ctrlWidth*2), ((keyboardHeight - keyGapH) - keyHeight) - ho, (ctrlWidth), (keyHeight)));
	keyrects.push_back(makeRect((lo + keyGapW*3 + ctrlWidth*3), ((keyboardHeight - keyGapH) - keyHeight) - ho, (spacebarWidth), (keyHeight)));
	keyrects.push_back(makeRect((lo + keyGapW*4 + ctrlWidth*3 + spacebarWidth), ((keyboardHeight - keyGapH) - keyHeight) - ho, (ctrlWidth), (keyHeight)));
	keyrects.push_back(makeRect((lo + keyGapW*5 + ctrlWidth*4 + spacebarWidth), ((keyboardHeight - keyGapH) - keyHeight) - ho, (ctrlWidth), (keyHeight)));
	keyrects.push_back(makeRect((lo + keyGapW*6 + ctrlWidth*5 + spacebarWidth), ((keyboardHeight - keyGapH) - keyHeight) - ho, (ctrlWidth), (keyHeight)));
	keyrects.push_back(makeRect((lo + keyGapW*7 + ctrlWidth*6 + spacebarWidth), ((keyboardHeight - keyGapH) - keyHeight) - ho, (bottomFnWidth), (keyHeight)));
	
	//row 6 arrow keys:
	keyrects.push_back(makeRect((lo + keyGapW*7 + ctrlWidth*6 + spacebarWidth + bottomFnWidth + keyGapWide), ((keyboardHeight - keyGapH) - keyHeight) - ho, (keyWidth), (keyHeight)));
	keyrects.push_back(makeRect((lo + keyGapW*8 + ctrlWidth*6 + spacebarWidth + bottomFnWidth + keyGapWide + keyWidth), ((keyboardHeight - keyGapH) - keyHeight) - ho, (keyWidth), (keyHeight)));
	keyrects.push_back(makeRect((lo + keyGapW*9 + ctrlWidth*6 + spacebarWidth + bottomFnWidth + keyGapWide + keyWidth*2), ((keyboardHeight - keyGapH) - keyHeight) - ho, (keyWidth), (keyHeight)));
	
	//row 6 numpad keys:
	keyrects.push_back(makeRect((lo + keyGapW*9 + ctrlWidth*6 + spacebarWidth + bottomFnWidth + keyGapWide*2 + keyWidth*3), ((keyboardHeight - keyGapH) - keyHeight) - ho, (backspaceWidth), (keyHeight)));
	keyrects.push_back(makeRect((lo + keyGapW*10 + ctrlWidth*6 + spacebarWidth + bottomFnWidth + keyGapWide*2 + keyWidth*3 + backspaceWidth), ((keyboardHeight - keyGapH) - keyHeight) - ho, (keyWidth), (keyHeight)));
	
	//row 5 main keys:
	keyrects.push_back(makeRect((lo), (keyboardHeight - (keyGapH*2 + keyHeight*2)) - ho, (leftShiftWidth), (keyHeight)));
	keyrects.push_back(makeRect((lo + keyGapW + leftShiftWidth), (keyboardHeight - (keyGapH*2 + keyHeight*2)) - ho, (keyWidth), (keyHeight)));
	keyrects.push_back(makeRect((lo + keyGapW*2 + leftShiftWidth + keyWidth), (keyboardHeight - (keyGapH*2 + keyHeight*2)) - ho, (keyWidth), (keyHeight)));
	keyrects.push_back(makeRect((lo + keyGapW*3 + leftShiftWidth + keyWidth*2), (keyboardHeight - (keyGapH*2 + keyHeight*2)) - ho, (keyWidth), (keyHeight)));
	keyrects.push_back(makeRect((lo + keyGapW*4 + leftShiftWidth + keyWidth*3), (keyboardHeight - (keyGapH*2 + keyHeight*2)) - ho, (keyWidth), (keyHeight)));
	keyrects.push_back(makeRect((lo + keyGapW*5 + leftShiftWidth + keyWidth*4), (keyboardHeight - (keyGapH*2 + keyHeight*2)) - ho, (keyWidth), (keyHeight)));
	keyrects.push_back(makeRect((lo + keyGapW*6 + leftShiftWidth + keyWidth*5), (keyboardHeight - (keyGapH*2 + keyHeight*2)) - ho, (keyWidth), (keyHeight)));
	keyrects.push_back(makeRect((lo + keyGapW*7 + leftShiftWidth + keyWidth*6), (keyboardHeight - (keyGapH*2 + keyHeight*2)) - ho, (keyWidth), (keyHeight)));
	keyrects.push_back(makeRect((lo + keyGapW*8 + leftShiftWidth + keyWidth*7), (keyboardHeight - (keyGapH*2 + keyHeight*2)) - ho, (keyWidth), (keyHeight)));
	keyrects.push_back(makeRect((lo + keyGapW*9 + leftShiftWidth + keyWidth*8), (keyboardHeight - (keyGapH*2 + keyHeight*2)) - ho, (keyWidth), (keyHeight)));
	keyrects.push_back(makeRect((lo + keyGapW*10 + leftShiftWidth + keyWidth*9), (keyboardHeight - (keyGapH*2 + keyHeight*2)) - ho, (keyWidth), (keyHeight)));
	keyrects.push_back(makeRect((lo + keyGapW*11 + leftShiftWidth + keyWidth*10), (keyboardHeight - (keyGapH*2 + keyHeight*2)) - ho, (shiftWidth), (keyHeight)));

	//row 5 arrow key:	
	keyrects.push_back(makeRect((lo + keyGapW*8 + ctrlWidth*6 + spacebarWidth + bottomFnWidth + keyGapWide + keyWidth), (keyboardHeight - (keyGapH*2 + keyHeight*2)) - ho, (keyWidth), (keyHeight)));
	
	//row 5 numpad keys:
	keyrects.push_back(makeRect((lo + keyGapW*9 + ctrlWidth*6 + spacebarWidth + bottomFnWidth + keyGapWide*2 + keyWidth*3), (keyboardHeight - (keyGapH*2 + keyHeight*2)) - ho, (keyWidth), (keyHeight)));
	keyrects.push_back(makeRect((lo + keyGapW*10 + ctrlWidth*6 + spacebarWidth + bottomFnWidth + keyGapWide*2 + keyWidth*4), (keyboardHeight - (keyGapH*2 + keyHeight*2)) - ho, (keyWidth), (keyHeight)));
	keyrects.push_back(makeRect((lo + keyGapW*11 + ctrlWidth*6 + spacebarWidth + bottomFnWidth + keyGapWide*2 + keyWidth*5), (keyboardHeight - (keyGapH*2 + keyHeight*2)) - ho, (keyWidth), (keyHeight)));
	keyrects.push_back(makeRect((lo + keyGapW*12 + ctrlWidth*6 + spacebarWidth + bottomFnWidth + keyGapWide*2 + keyWidth*6), (keyboardHeight - (keyGapH*2 + keyHeight*2)) - ho, (keyWidth), (verticalHeight)));
	
	//row 4 main keys:
	keyrects.push_back(makeRect((lo), (keyboardHeight - (keyGapH*3 + keyHeight*3)) - ho, (capsWidth), (keyHeight)));
	keyrects.push_back(makeRect((lo + keyGapW + capsWidth), (keyboardHeight - (keyGapH*3 + keyHeight*3)) - ho, (keyWidth), (keyHeight)));
	keyrects.push_back(makeRect((lo + keyGapW*2 + capsWidth + keyWidth), (keyboardHeight - (keyGapH*3 + keyHeight*3)) - ho, (keyWidth), (keyHeight)));
	keyrects.push_back(makeRect((lo + keyGapW*3 + capsWidth + keyWidth*2), (keyboardHeight - (keyGapH*3 + keyHeight*3)) - ho, (keyWidth), (keyHeight)));
	keyrects.push_back(makeRect((lo + keyGapW*4 + capsWidth + keyWidth*3), (keyboardHeight - (keyGapH*3 + keyHeight*3)) - ho, (keyWidth), (keyHeight)));
	keyrects.push_back(makeRect((lo + keyGapW*5 + capsWidth + keyWidth*4), (keyboardHeight - (keyGapH*3 + keyHeight*3)) - ho, (keyWidth), (keyHeight)));
	keyrects.push_back(makeRect((lo + keyGapW*6 + capsWidth + keyWidth*5), (keyboardHeight - (keyGapH*3 + keyHeight*3)) - ho, (keyWidth), (keyHeight)));
	keyrects.push_back(makeRect((lo + keyGapW*7 + capsWidth + keyWidth*6), (keyboardHeight - (keyGapH*3 + keyHeight*3)) - ho, (keyWidth), (keyHeight)));
	keyrects.push_back(makeRect((lo + keyGapW*8 + capsWidth + keyWidth*7), (keyboardHeight - (keyGapH*3 + keyHeight*3)) - ho, (keyWidth), (keyHeight)));
	keyrects.push_back(makeRect((lo + keyGapW*9 + capsWidth + keyWidth*8), (keyboardHeight - (keyGapH*3 + keyHeight*3)) - ho, (keyWidth), (keyHeight)));
	keyrects.push_back(makeRect((lo + keyGapW*10 + capsWidth + keyWidth*9), (keyboardHeight - (keyGapH*3 + keyHeight*3)) - ho, (keyWidth), (keyHeight)));
	keyrects.push_back(makeRect((lo + keyGapW*11 + capsWidth + keyWidth*10), (keyboardHeight - (keyGapH*3 + keyHeight*3)) - ho, (keyWidth), (keyHeight)));
	keyrects.push_back(makeRect((lo + keyGapW*12 + capsWidth + keyWidth*11), (keyboardHeight - (keyGapH*3 + keyHeight*3)) - ho, (leftShiftWidth), (keyHeight)));
	
	//row 4 numpad:
	keyrects.push_back(makeRect((lo + keyGapW*9 + ctrlWidth*6 + spacebarWidth + bottomFnWidth + keyGapWide*2 + keyWidth*3), (keyboardHeight - (keyGapH*3 + keyHeight*3)) - ho, (keyWidth), (keyHeight)));
	keyrects.push_back(makeRect((lo + keyGapW*10 + ctrlWidth*6 + spacebarWidth + bottomFnWidth + keyGapWide*2 + keyWidth*4), (keyboardHeight - (keyGapH*3 + keyHeight*3)) - ho, (keyWidth), (keyHeight)));
	keyrects.push_back(makeRect((lo + keyGapW*11 + ctrlWidth*6 + spacebarWidth + bottomFnWidth + keyGapWide*2 + keyWidth*5), (keyboardHeight - (keyGapH*3 + keyHeight*3)) - ho, (keyWidth), (keyHeight)));
	
	//row 3 main keys:
	keyrects.push_back(makeRect((lo), (keyboardHeight - (keyGapH*4 + keyHeight*4)) - ho, (tabWidth), (keyHeight)));
	keyrects.push_back(makeRect((lo + keyGapW + tabWidth), (keyboardHeight - (keyGapH*4 + keyHeight*4)) - ho, (keyWidth), (keyHeight)));
	keyrects.push_back(makeRect((lo + keyGapW*2 + tabWidth + keyWidth), (keyboardHeight - (keyGapH*4 + keyHeight*4)) - ho, (keyWidth), (keyHeight)));
	keyrects.push_back(makeRect((lo + keyGapW*3 + tabWidth + keyWidth*2), (keyboardHeight - (keyGapH*4 + keyHeight*4)) - ho, (keyWidth), (keyHeight)));
	keyrects.push_back(makeRect((lo + keyGapW*4 + tabWidth + keyWidth*3), (keyboardHeight - (keyGapH*4 + keyHeight*4)) - ho, (keyWidth), (keyHeight)));
	keyrects.push_back(makeRect((lo + keyGapW*5 + tabWidth + keyWidth*4), (keyboardHeight - (keyGapH*4 + keyHeight*4)) - ho, (keyWidth), (keyHeight)));
	keyrects.push_back(makeRect((lo + keyGapW*6 + tabWidth + keyWidth*5), (keyboardHeight - (keyGapH*4 + keyHeight*4)) - ho, (keyWidth), (keyHeight)));
	keyrects.push_back(makeRect((lo + keyGapW*7 + tabWidth + keyWidth*6), (keyboardHeight - (keyGapH*4 + keyHeight*4)) - ho, (keyWidth), (keyHeight)));
	keyrects.push_back(makeRect((lo + keyGapW*8 + tabWidth + keyWidth*7), (keyboardHeight - (keyGapH*4 + keyHeight*4)) - ho, (keyWidth), (keyHeight)));
	keyrects.push_back(makeRect((lo + keyGapW*9 + tabWidth + keyWidth*8), (keyboardHeight - (keyGapH*4 + keyHeight*4)) - ho, (keyWidth), (keyHeight)));
	keyrects.push_back(makeRect((lo + keyGapW*10 + tabWidth + keyWidth*9), (keyboardHeight - (keyGapH*4 + keyHeight*4)) - ho, (keyWidth), (keyHeight)));
	keyrects.push_back(makeRect((lo + keyGapW*11 + tabWidth + keyWidth*10), (keyboardHeight - (keyGapH*4 + keyHeight*4)) - ho, (keyWidth), (keyHeight)));
	keyrects.push_back(makeRect((lo + keyGapW*12 + tabWidth + keyWidth*11), (keyboardHeight - (keyGapH*4 + keyHeight*4)) - ho, (keyWidth), (keyHeight)));
	keyrects.push_back(makeRect((lo + keyGapW*13 + tabWidth + keyWidth*12), (keyboardHeight - (keyGapH*4 + keyHeight*4)) - ho, (tabWidth), (keyHeight)));
	
	//row 3 island keys:
	keyrects.push_back(makeRect((lo + keyGapW*7 + ctrlWidth*6 + spacebarWidth + bottomFnWidth + keyGapWide), (keyboardHeight - (keyGapH*4 + keyHeight*4)) - ho, (keyWidth), (keyHeight)));
	keyrects.push_back(makeRect((lo + keyGapW*8 + ctrlWidth*6 + spacebarWidth + bottomFnWidth + keyGapWide + keyWidth), (keyboardHeight - (keyGapH*4 + keyHeight*4)) - ho, (keyWidth), (keyHeight)));
	keyrects.push_back(makeRect((lo + keyGapW*9 + ctrlWidth*6 + spacebarWidth + bottomFnWidth + keyGapWide + keyWidth*2), (keyboardHeight - (keyGapH*4 + keyHeight*4)) - ho, (keyWidth), (keyHeight)));
	
	//row 3 numpad keys:
	keyrects.push_back(makeRect((lo + keyGapW*9 + ctrlWidth*6 + spacebarWidth + bottomFnWidth + keyGapWide*2 + keyWidth*3), (keyboardHeight - (keyGapH*4 + keyHeight*4)) - ho, (keyWidth), (keyHeight)));
	keyrects.push_back(makeRect((lo + keyGapW*10 + ctrlWidth*6 + spacebarWidth + bottomFnWidth + keyGapWide*2 + keyWidth*4), (keyboardHeight - (keyGapH*4 + keyHeight*4)) - ho, (keyWidth), (keyHeight)));
	keyrects.push_back(makeRect((lo + keyGapW*11 + ctrlWidth*6 + spacebarWidth + bottomFnWidth + keyGapWide*2 + keyWidth*5), (keyboardHeight - (keyGapH*4 + keyHeight*4)) - ho, (keyWidth), (keyHeight)));
	keyrects.push_back(makeRect((lo + keyGapW*12 + ctrlWidth*6 + spacebarWidth + bottomFnWidth + keyGapWide*2 + keyWidth*6), (keyboardHeight - (keyGapH*4 + keyHeight*4)) - ho, (keyWidth), (verticalHeight)));
	
	//row 2 main keys:
	keyrects.push_back(makeRect((lo), (keyboardHeight - (keyGapH*5 + keyHeight*5)) - ho, (keyWidth), (keyHeight)));
	keyrects.push_back(makeRect((lo + keyGapW + keyWidth), (keyboardHeight - (keyGapH*5 + keyHeight*5)) - ho, (keyWidth), (keyHeight)));
	keyrects.push_back(makeRect((lo + keyGapW*2 + keyWidth*2), (keyboardHeight - (keyGapH*5 + keyHeight*5)) - ho, (keyWidth), (keyHeight)));
	keyrects.push_back(makeRect((lo + keyGapW*3 + keyWidth*3), (keyboardHeight - (keyGapH*5 + keyHeight*5)) - ho, (keyWidth), (keyHeight)));
	keyrects.push_back(makeRect((lo + keyGapW*4 + keyWidth*4), (keyboardHeight - (keyGapH*5 + keyHeight*5)) - ho, (keyWidth), (keyHeight)));
	keyrects.push_back(makeRect((lo + keyGapW*5 + keyWidth*5), (keyboardHeight - (keyGapH*5 + keyHeight*5)) - ho, (keyWidth), (keyHeight)));
	keyrects.push_back(makeRect((lo + keyGapW*6 + keyWidth*6), (keyboardHeight - (keyGapH*5 + keyHeight*5)) - ho, (keyWidth), (keyHeight)));
	keyrects.push_back(makeRect((lo + keyGapW*7 + keyWidth*7), (keyboardHeight - (keyGapH*5 + keyHeight*5)) - ho, (keyWidth), (keyHeight)));
	keyrects.push_back(makeRect((lo + keyGapW*8 + keyWidth*8), (keyboardHeight - (keyGapH*5 + keyHeight*5)) - ho, (keyWidth), (keyHeight)));
	keyrects.push_back(makeRect((lo + keyGapW*9 + keyWidth*9), (keyboardHeight - (keyGapH*5 + keyHeight*5)) - ho, (keyWidth), (keyHeight)));
	keyrects.push_back(makeRect((lo + keyGapW*10 + keyWidth*10), (keyboardHeight - (keyGapH*5 + keyHeight*5)) - ho, (keyWidth), (keyHeight)));
	keyrects.push_back(makeRect((lo + keyGapW*11 + keyWidth*11), (keyboardHeight - (keyGapH*5 + keyHeight*5)) - ho, (keyWidth), (keyHeight)));
	keyrects.push_back(makeRect((lo + keyGapW*12 + keyWidth*12), (keyboardHeight - (keyGapH*5 + keyHeight*5)) - ho, (keyWidth), (keyHeight)));
	keyrects.push_back(makeRect((lo + keyGapW*13 + keyWidth*13), (keyboardHeight - (keyGapH*5 + keyHeight*5)) - ho, (backspaceWidth), (keyHeight)));
	
	//row 2 island keys:
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
	
	return organizedRects;
}

physicalLayout::keyRect physicalLayout::makeRect(float x, float y, float w, float h){
	physicalLayout::keyRect kr;
	kr.x = static_cast<int>(x);
	kr.y = static_cast<int>(y);
	kr.w = static_cast<int>(w);
	kr.h = static_cast<int>(h);
	return kr;
}
